jaycollett/MQTT-Button/Project Images/20190307_212025.jpg

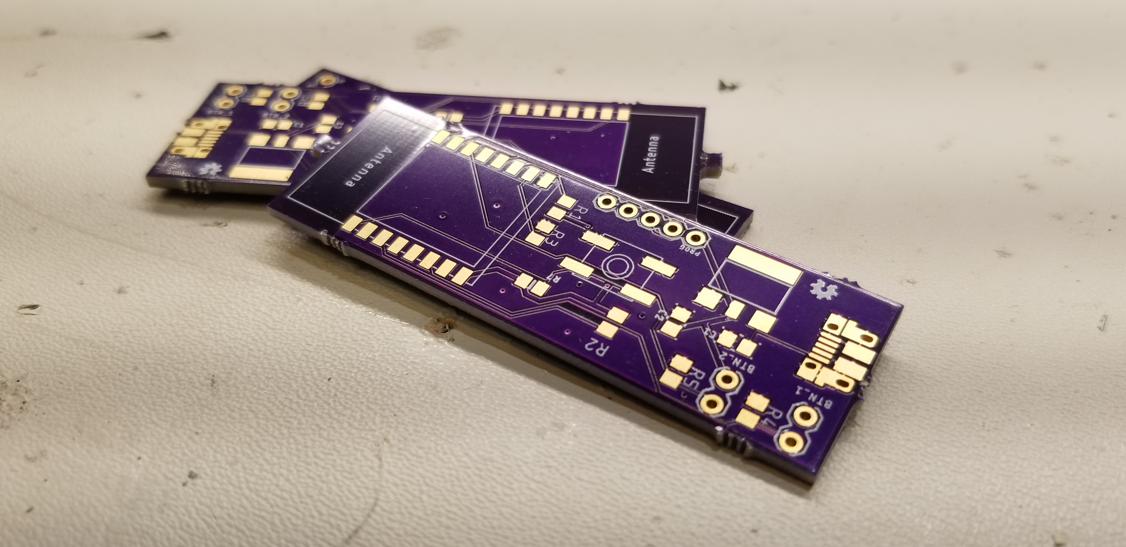
Project Images/20190307_212025.jpg
