jaycollett/MQTT-Button/Project Images/20190307_212216.jpg

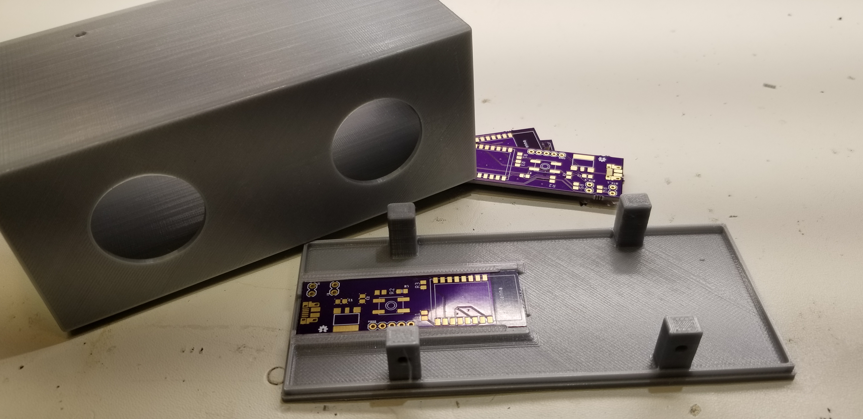
Project Images/20190307_212216.jpg
