jaycollett/MQTT-Button/Project Images/20190308_104159.jpg

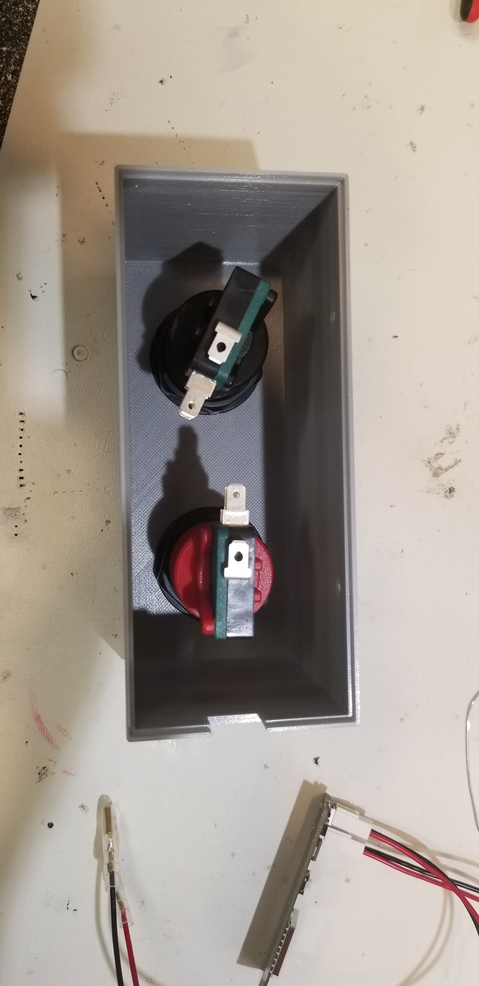
Project Images/20190308_104159.jpg
