jaycollett/MQTT-Button/Project Images/20190308_104226.jpg

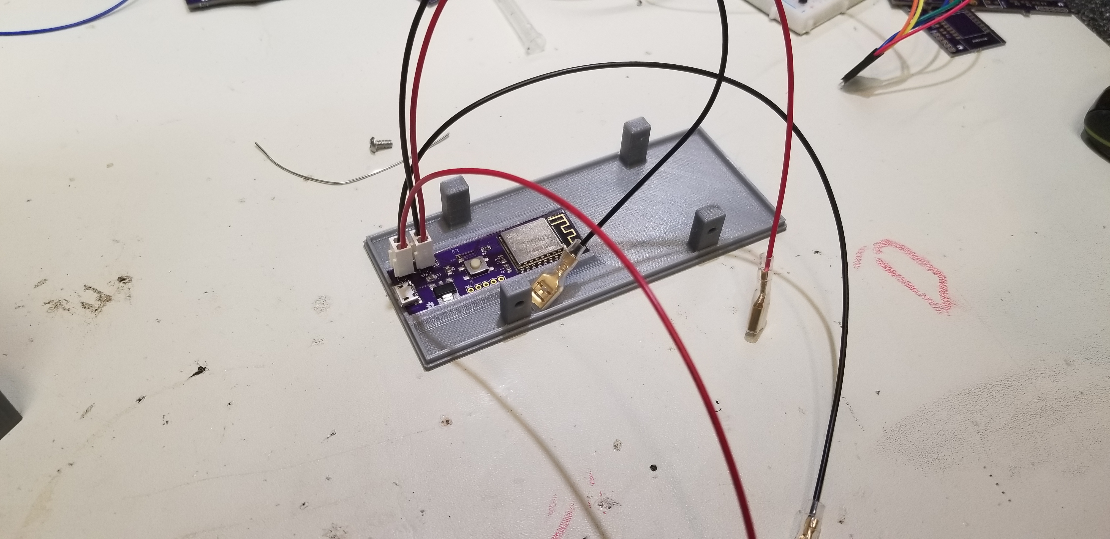
Project Images/20190308_104226.jpg
