jaycollett/MQTT-Button/Project Images/20190308_104546-4.jpg

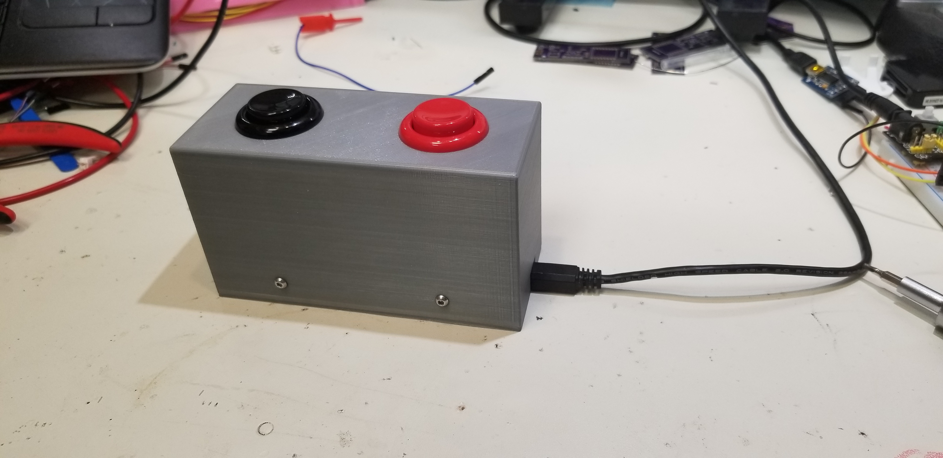
Project Images/20190308_104546-4.jpg
